ahessling/ActiveLoad/Firmware/driver/DOGS104.hpp

/**
 * @file DOGS104.hpp
 *
 * @date 13.02.2016
 * @author Andre
 * @description
 */
#ifndef DOGS104_HPP_
#define DOGS104_HPP_

#include <stdint.h>
#include <errno.h>

/** Electronic Assembly DOGS104 display base class.
 *
 * This class implements the high level functions.
 * The low level interface functions (SPI or I2C) need
 * to be implemented by a derivative class.
 */
class DOGS104
{
public:

  /** Font width */
  enum DogFontWidth
  {
    FONT_WIDTH_5 = 0, //!< 5-dot font width
    FONT_WIDTH_6      //!< 6-dot font width
  };

  /** Number of display lines */
  enum DogDisplayLines
  {
    LINES_1 = 0,   //!< 1-line display
    LINES_2,       //!< 2-lines display
    LINES_3,       //!< 3-lines display
    LINES_4        //!< 4-lines display
  };

  DOGS104(enum DogFontWidth fontWidth, enum DogDisplayLines lines,
      bool topView = false);
  virtual ~DOGS104() { }

  void init();

  void setContrast(unsigned char contrast);

  void clear();

  void write(unsigned char c);

  int write(unsigned char c, unsigned char x, unsigned char y);

  int write(char* str);

  int write(char* str, unsigned char x, unsigned char y);

  int gotoXY(unsigned char x, unsigned char y);

  void setDoubleBuffered(bool doubleBuffered);

  virtual void refresh();

  /** Perform a read operation.
   *
   * @param rs RS bit
   * @return read value
   */
  virtual char read(bool rs) { return 0; }

protected:
  virtual void reset() = 0;

  virtual int writeCommand(uint16_t command) = 0;

private:
  void setDDRAMAddress(unsigned char address);
  int _gotoXY(unsigned char x, unsigned char y);

  enum DogFontWidth _fontWidth;
  enum DogDisplayLines _lines;
  bool _topView;
  bool _doubleBuffered; ///< Double buffered on/off
  char _frameBuffer[40]; ///< Frame buffer in double buffered configuration
  unsigned char _cursorPos; ///< Current cursor position
  unsigned char _dirtyFrom; ///< First position of changed data in framebuffer
  unsigned char _dirtyTo; ///< Last position of changed data in framebuffer
  bool _dirty;
  unsigned char _functionSet; ///< Value of function set register (often needed)
};

#endif /* DOGS104_HPP_ */
